perezbecker/halloween_bucket/renders/02_front.png

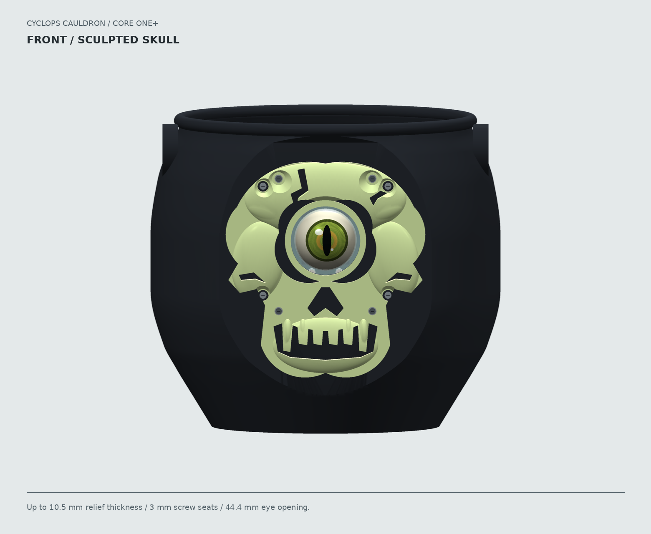
renders/02_front.png
