perezbecker/halloween_bucket/renders/03_rear.png

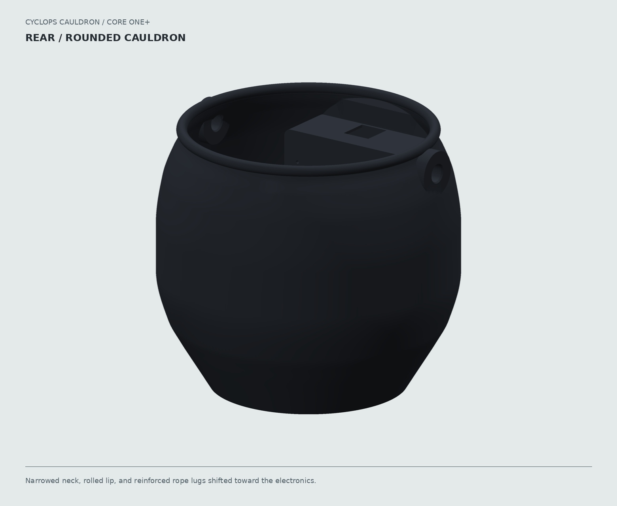
renders/03_rear.png
