perezbecker/halloween_bucket/renders/05_cutaway.png

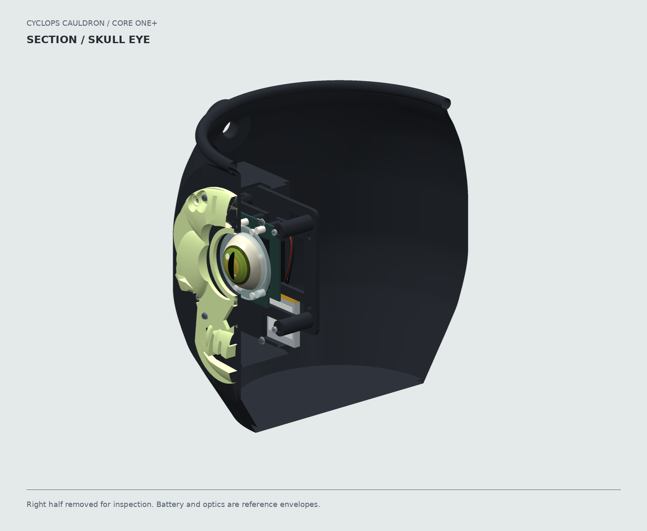
renders/05_cutaway.png
