perezbecker/halloween_bucket/renders/07_exploded_mount.png

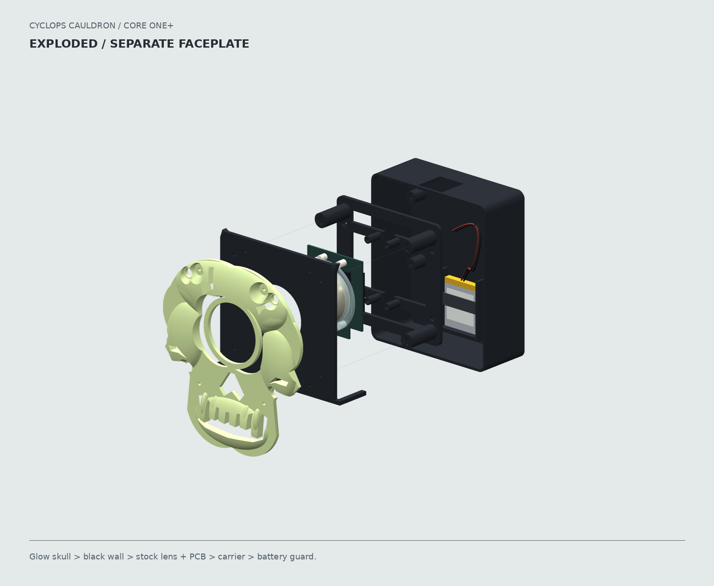
renders/07_exploded_mount.png
