perezbecker/halloween_bucket/renders/08_glow_preview.png

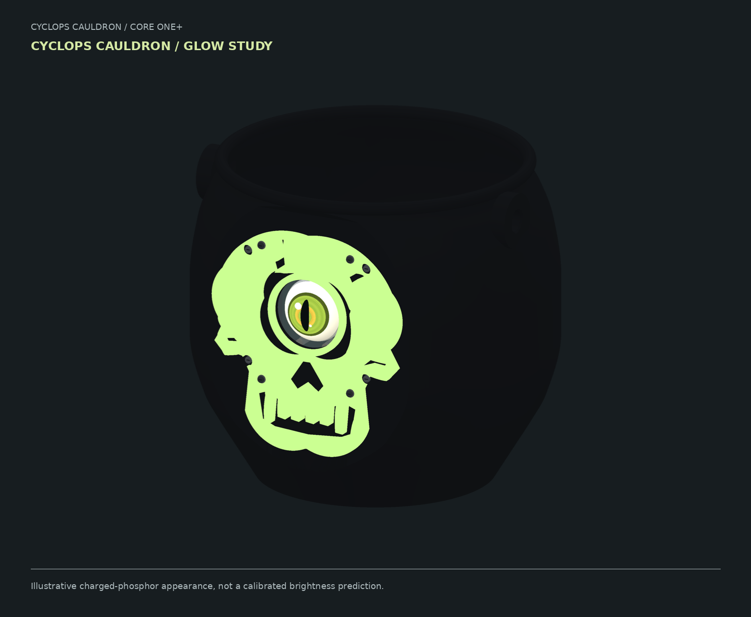
renders/08_glow_preview.png
