perezbecker/halloween_bucket/renders/10_rope_balance.png

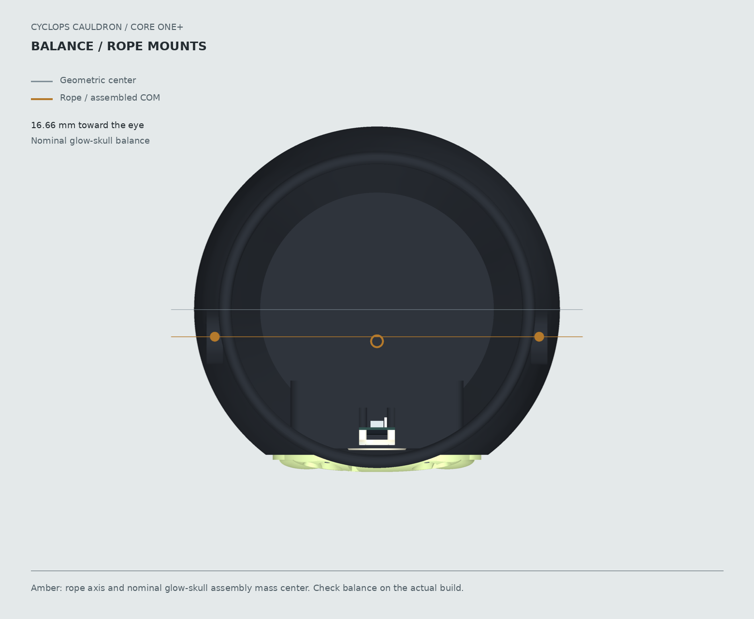
renders/10_rope_balance.png
