perezbecker/halloween_bucket/renders/11_sculpted_closeup.png

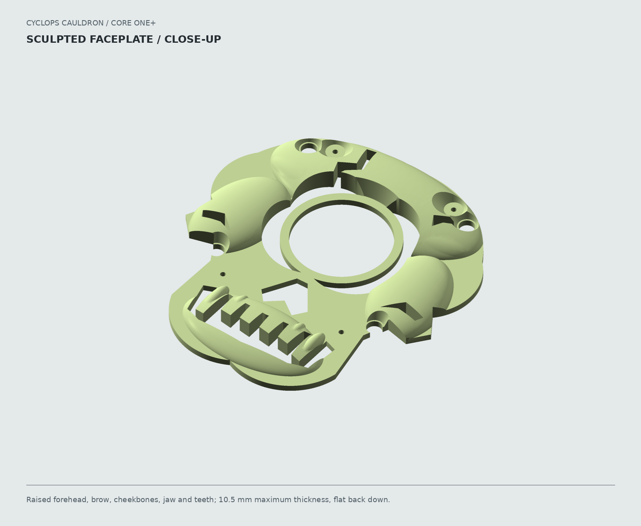
renders/11_sculpted_closeup.png
