perezbecker/halloween_bucket/renders/12_sculpted_front.png

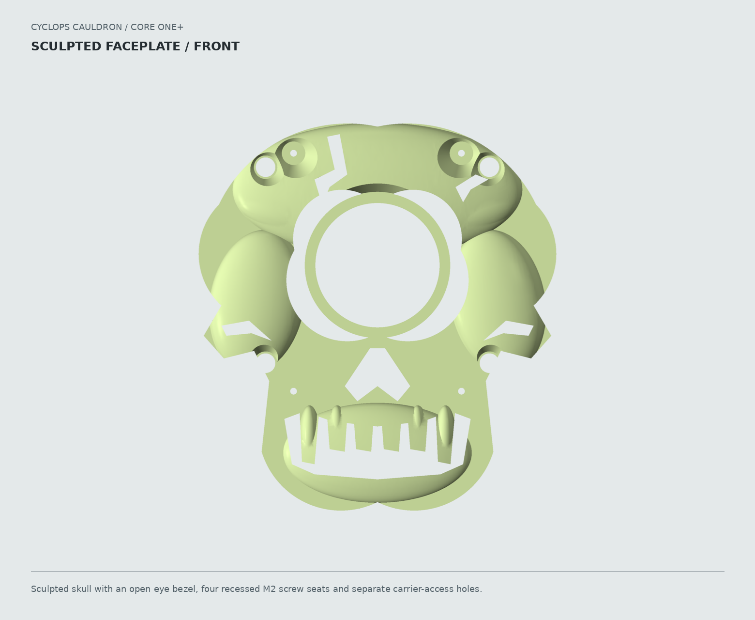
renders/12_sculpted_front.png
