perezbecker/halloween_bucket/renders/13_sculpted_raking.png

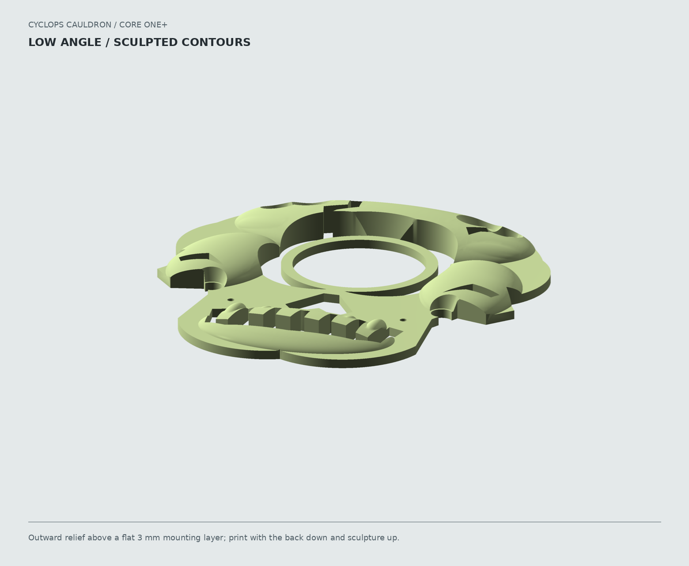
renders/13_sculpted_raking.png
