perezbecker/halloween_bucket/renders/overview.png

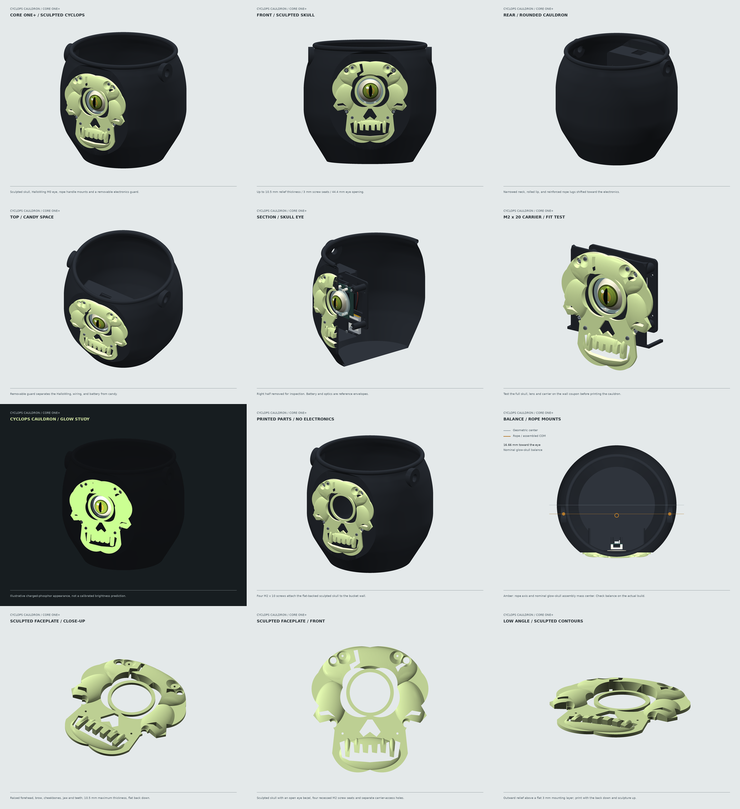
renders/overview.png
