perezbecker/halloween_bucket/renders/print_beds/03_carrier_black.png

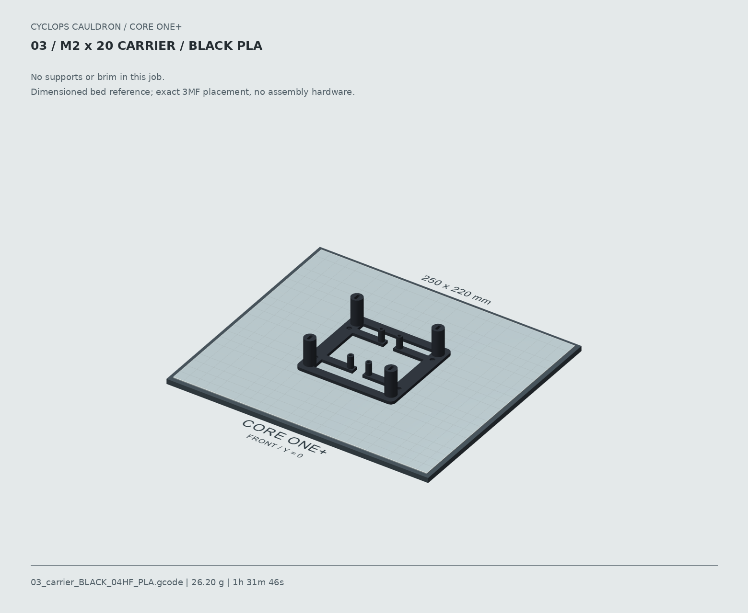
renders/print_beds/03_carrier_black.png
